Neutree/Gimbal/embedded/demo/MDK/offchip/stm32103c8t6/app/Gimbal.cpp

#include "Gimbal.h"


Gimbal::Gimbal(InertialSensor& ins,Magnetometer& mag,BLDCMotor& motorRoll,BLDCMotor& motorPitch,BLDCMotor& motorYaw,ADC& adc,uint8_t voltageChannel,uint8_t yawResChannel,flash& flash_)
:mIns(ins),mMag(&mag),mMotorRoll(motorRoll),mMotorPitch(motorPitch),mMotorYaw(motorYaw),mADC(adc),mParameter(flash_),mVoltageChannel(voltageChannel),mYawValueChannel(yawResChannel),mIsGyroCalibrating(false),mYawMode(1)
{
	mIsArmed = false;
	mTargetAngle(0,0,0);
	mTargetAngleTemp(0,0,0);
}
bool Gimbal::Init(uint8_t yawSensorType)
{
	float time = TaskManager::Time();
	bool isInitSuccess=true;
	if(!mIns.Init(true))
		isInitSuccess = false;
	//初始化磁力计
	if(!mMag->Init(true))
		isInitSuccess = false;
	
	//从flash中读取参数
	if(!ReadParam2Flash())
	{
		mPIDRoll(5,0.2,0.6);
		mPIDPitch(5,0.1,0.2);
		mPIDYaw(5,0.1,0.1);
		mIns.SetGyrOffset(0,0,0);
		mMag->SetOffsetRatio(1.285,1.285,1);
		mMag->SetOffsetBias(236,309,114);
		//保存信息到flash
		SaveParam2Flash();
	}
	CheckMotorDisable();
	mYawSensorType = yawSensorType;
	if(mYawSensorType == 1)
		mYawAngleRes = GetYawValue()/(2.3-0.35)*260.0 ;
	return isInitSuccess;
}
bool Gimbal::UpdateIMU()
{
	if(MOD_ERROR== mIns.Update())
	{
		LOG("mpu6050 error\n\n\n");
		return false;
	}
	if(mMag!=0)
	{
		if(MOD_ERROR == mMag->Update())
		{
			LOG("MAG error\n\n\n");
			return false;
		}
	}
	if(mIsGyroCalibrating&&mIns.IsGyroCalibrated())//角速度校准刚结束
	{
		mIsGyroCalibrating = false;
		LOG("\ngyro calibrate complete\n");
		SaveParam2Flash();
		mMotorRoll.Enable();
		mMotorPitch.Enable();
		mMotorYaw.Enable();
	}
	
	if(mIsMagCalibrating&&mMag->IsCalibrated())//磁力计校准刚结束
	{
		mIsMagCalibrating = false;
		LOG("\nmagnetometer calibrate complete\n");
		SaveParam2Flash();
	}
	
	if(mIns.IsGyroCalibrated())//角速度和磁力计已经校准了
	{		
		if(mYawSensorType==1)//电位器+加速度角速度计
		{
//				mAngle = mAHRS_Algorithm.GetAngleMahony(mIns.GetAccRaw(),mIns.GetGyr(),mMag->GetDataRaw(),mIns.GetUpdateInterval());
//			Vector3<int> mag0(0,0,0);
//			mAngle = mAHRS_Algorithm.GetAngleMahony(mIns.GetAccRaw(),mIns.GetGyr(),mag0,mIns.GetUpdateInterval());
			mAngle = mAHRS_Algorithm.GetAngleDCM(mIns.GetAcc(),mIns.GetGyr(),mIns.GetUpdateInterval());
			if(mYawMode == 2)//静止模式
			{
				mYawAngleRes = mYawAngleRes*0.998 + ( GetYawValue()/(2.3-0.35)*260.0 )*0.002;//高斯滤波
				mAngle.z = mYawAngleRes;
			}
			else if(mYawMode == 1)//跟随模式
			{

				mYawAngleRes = mYawAngleRes*0.998 + ( GetYawValue()/(2.3-0.35)*260.0 )*0.002;//高斯滤波
				mAngle.z = mYawAngleRes;
			}
			else if(mYawMode ==  3)//绝对静止模式
			{
				
			}
		}
		else if(mYawSensorType==2)//电位器+IMU+磁力计
		{
			if(mMag->IsCalibrated())
			{
					mAngle = mAHRS_Algorithm.GetAngleMahony(mIns.GetAccRaw(),mIns.GetGyr(), mMag->GetDataRaw(),mIns.GetUpdateInterval());
			}
		}
		//根据传感器安装方位进行换向
		mAngle.z = -mAngle.z;
//		mAngle.y>0?(mAngle.y-=180):(mAngle.y+=180);
//		mAngle.y = -mAngle.y;
		mAngle.z>0?(mAngle.z-=180):(mAngle.z+=180);
		
		//转换为弧度
		mAngle*=AtR;
//		mAngle2*=AtR;
	}
	return true;
}
float Gimbal::GetYawValue()
{
	return mADC[mYawValueChannel];
}
bool Gimbal::UpdateMotor(int* motorRollValue,int* motorPitchValue, int* motorYawValue)
{
	static int v=0,v2=0,v3=0;
	mTargetAngleTemp = mTargetAngleTemp*0.998 + mTargetAngle*0.002;
	v  = mPIDRoll.Controll(mTargetAngleTemp.y,mAngle.y);
	v2 = mPIDPitch.Controll(mTargetAngleTemp.x,mAngle.x);
	if(mYawMode == 2)//相对静止模式
		v3 = mPIDYaw.Controll(mTargetAngleTemp.z,mAngle.z);
	else if(mYawMode == 1)//跟随模式
	{
		//根据云台的姿态求出z轴的角速度
		float yawVel = cos(mAngle.y)*cos(mAngle.x)*mIns.GetGyr().z - mIns.GetGyr().y*sin(mAngle.y) + mIns.GetGyr().x*sin(mAngle.y)*sin(mAngle.x);
		static float kd=0;
		kd=mPIDYaw.mKd;
		mPIDYaw.mKd = 0;
		yaw__ = yawVel*kd*100;
		v3 = mPIDYaw.Controll(mTargetAngle.z,mAngle.z)+yaw__;
		mPIDYaw.mKd = kd;
	}
	else if(mYawMode == 3)//绝对静止模式
	{
		
	}
	v3=-v3;
	if(mMotorRoll.IsEnabled())
		mMotorRoll.SetPosition(v);
	if(mMotorPitch.IsEnabled())
		mMotorPitch.SetPosition(v2);
	if(mMotorYaw.IsEnabled())
		mMotorYaw.SetPosition(v3);
	
	if(motorRollValue!=0)
		*motorRollValue = v;
	if(motorPitchValue!=0)
		*motorPitchValue = v2;
	if(motorYawValue!=0)
		*motorYawValue = v3;
	return true;
}
float Gimbal::UpdateVoltage(float resister_a,float resister_b,float fullRange)
{
	return mADC.Voltage_I(mVoltageChannel,resister_a,resister_b,fullRange);
}
bool Gimbal::IsGyroCalibrated()
{
	return mIns.IsGyroCalibrated();
}
bool Gimbal::IsGyroCalibrating()
{
	return mIsGyroCalibrating;
}
void Gimbal::StartGyroCalibrate()
{
	mMotorRoll.Disable();
	mMotorPitch.Disable();
	mMotorYaw.Disable();
	float time = TaskManager::Time();
	while(TaskManager::Time()-time<2.5)
	{
		if(MOD_ERROR== mIns.Update())
		{
			LOG("mpu6050 error\n\n\n");
			return;
		}
		if(mMag!=0)
		{
			if(MOD_ERROR == mMag->Update())
			{
				LOG("MAG error\n\n\n");
				return ;
			}
		}
		TaskManager::DelayMs(100);
	}	
	mIns.StartGyroCalibrate();//启动校准
	mIsGyroCalibrating = true;
	LOG("start gyro calibrate, don't move\n");
}
bool Gimbal::IsMagCalibrated()
{
	return mMag->IsCalibrated();
}
bool Gimbal::IsMagCalibrating()
{
	return mIsMagCalibrating;
}
void Gimbal::StartMagCalibrate()
{
	mMag->StartCalibrate();//启动校准
	mIsMagCalibrating = true;
	LOG("magnetometer is calibrating ... don't move!!!\n");
}
void Gimbal::CheckMotorDisable()
{
	if(mMotorRoll.IsEnabled())
	{
		if(mPIDRoll.mKp==0 && mPIDRoll.mKi==0 && mPIDRoll.mKd==0)
		{
			mPIDRoll.Clear();
			mMotorRoll.Disable();
		}
	}
	else
	{
		if(mPIDRoll.mKp!=0 || mPIDRoll.mKi!=0 || mPIDRoll.mKd!=0)
			mMotorRoll.Enable();
	}
	if(mMotorPitch.IsEnabled())
	{
		if(mPIDPitch.mKp==0 && mPIDPitch.mKi==0 && mPIDPitch.mKd==0)
		{
			mPIDPitch.Clear();
			mMotorPitch.Disable();
		}
	}
	else
	{
		if(mPIDPitch.mKp!=0 || mPIDPitch.mKi!=0 || mPIDPitch.mKd!=0)
			mMotorPitch.Enable();
	}
	if(mMotorYaw.IsEnabled())
	{
		if(mPIDYaw.mKp==0 && mPIDYaw.mKi==0 && mPIDYaw.mKd==0)
		{
			mPIDYaw.Clear();
			mMotorYaw.Disable();
		}
	}
	else
	{
		if(mPIDYaw.mKp!=0 || mPIDYaw.mKi!=0 || mPIDYaw.mKd!=0)
			mMotorYaw.Enable();
	}
}
bool Gimbal::SaveParam2Flash()
{
	// u16 data[20];
	// data[0] = 0x00aa;
	// data[1] = 0x00bb;
	// data[2] = mPIDRoll.mKp*1000;
	// data[3] = mPIDRoll.mKi*1000;
	// data[4] = mPIDRoll.mKd*1000;
	// data[5] = mPIDPitch.mKp*1000;
	// data[6] = mPIDPitch.mKi*1000;
	// data[7] = mPIDPitch.mKd*1000;
	// data[8] = mPIDYaw.mKp*1000;
	// data[9] = mPIDYaw.mKi*1000;
	// data[10] = mPIDYaw.mKd*1000;
	// data[11] = mIns.GetGyrOffset().x+32768;
	// data[12] = mIns.GetGyrOffset().y+32768;
	// data[13] = mIns.GetGyrOffset().z+32768;
	// data[14] = mMag->GetOffsetRatio().x*10000;
	// data[15] = mMag->GetOffsetRatio().y*10000;
	// data[16] = mMag->GetOffsetRatio().z*10000;
	// data[17] = mMag->GetOffsetBias().x+32768;
	// data[18] = mMag->GetOffsetBias().y+32768;
	// data[19] = mMag->GetOffsetBias().z+32768;
	// mFlash.Clear(0);
	// if(!mFlash.Write(0,0,data,20))
	// 	return false;
	// ReadParam2Flash();
	CheckMotorDisable();
	mPIDYaw.mKp*=0.01;
	mPIDYaw.mKi*=0.01;
	mPIDYaw.mKd*=0.01;
	return mParameter.SaveParam2Flash(mPIDRoll,mPIDPitch,mPIDYaw,mIns.GetGyrOffset(),mMag->GetOffsetRatio(),mMag->GetOffsetBias());
}

bool Gimbal::ReadPIDParam2Flash()
{
	// u16 data[11];
	// if(!mFlash.Read(0,0,data,11))
	// 	return false;
	// if(data[0]!=0x00aa || data[1]!=0x00bb)
	// 	return false;
	// mPIDRoll.SetKp(data[2]/1000.0);
	// mPIDRoll.SetKi(data[3]/1000.0);
	// mPIDRoll.SetKd(data[4]/1000.0);
	// mPIDPitch.SetKp(data[5]/1000.0);
	// mPIDPitch.SetKi(data[6]/1000.0);
	// mPIDPitch.SetKd(data[7]/1000.0);
	// mPIDYaw.SetKp(data[8]/1000.0);
	// mPIDYaw.SetKi(data[9]/1000.0);
	// mPIDYaw.SetKd(data[10]/1000.0);
	return false;
}
bool Gimbal::ReadGyroOffset2Flash()
{
	// u16 data[3];
	// if(!mFlash.Read(0,0,data,2))
	// 	return false;
	// if(data[0]!=0x00aa || data[1]!=0x00bb)
	// 	return false;
	// if(!mFlash.Read(0,11,data,3))
	// 	return false;
	// Vector3<int> gyroOffset;
	// gyroOffset.x = data[0]-32768;
	// gyroOffset.y = data[1]-32768;
	// gyroOffset.z = data[2]-32768;
	// mIns.SetGyrOffset(gyroOffset.x,gyroOffset.y,gyroOffset.z); 
	return false;
}
//磁力计校准值储存
bool Gimbal::ReadMagOffset2Flash()
{
	// u16 data[6];
	// if(!mFlash.Read(0,0,data,2))
	// 	return false;
	// if(data[0]!=0x00aa || data[1]!=0x00bb)
	// 	return false;
	// if(!mFlash.Read(0,14,data,6))
	// 	return false;
	// Vector3f magOffsetRatio,magOffsetBias;
	// magOffsetRatio.x = data[0]/10000.0;
	// magOffsetRatio.y = data[1]/10000.0;
	// magOffsetRatio.z = data[2]/10000.0;
	// magOffsetBias.x = data[3]-32768;
	// magOffsetBias.y = data[4]-32768;
	// magOffsetBias.z = data[5]-32768;
	// mMag->SetOffsetRatio(magOffsetRatio.x,magOffsetRatio.y,magOffsetRatio.z); 
	// mMag->SetOffsetBias(magOffsetBias.x,magOffsetBias.y,magOffsetBias.z);
	return false;
}

bool Gimbal::ReadParam2Flash()
{
	// u16 data[20];
	// if(!mFlash.Read(0,0,data,20))
	// 	return false;
	// if(data[0]!=0x00aa || data[1]!=0x00bb)
	// 	return false;
	// mPIDRoll.SetKp(data[2]/1000.0);
	// mPIDRoll.SetKi(data[3]/1000.0);
	// mPIDRoll.SetKd(data[4]/1000.0);
	// mPIDPitch.SetKp(data[5]/1000.0);
	// mPIDPitch.SetKi(data[6]/1000.0);
	// mPIDPitch.SetKd(data[7]/1000.0);
	// mPIDYaw.SetKp(data[8]/1000.0);
	// mPIDYaw.SetKi(data[9]/1000.0);
	// mPIDYaw.SetKd(data[10]/1000.0);
	// Vector3<int> gyroOffset;
	// gyroOffset.x = data[11]-32768;
	// gyroOffset.y = data[12]-32768;
	// gyroOffset.z = data[13]-32768;
	// mIns.SetGyrOffset(gyroOffset.x,gyroOffset.y,gyroOffset.z); 
	// Vector3f magOffsetRatio,magOffsetBias;
	// magOffsetRatio.x = data[14]/10000.0;
	// magOffsetRatio.y = data[15]/10000.0;
	// magOffsetRatio.z = data[16]/10000.0;
	// magOffsetBias.x = data[17]-32768;
	// magOffsetBias.y = data[18]-32768;
	// magOffsetBias.z = data[19]-32768;
	// mMag->SetOffsetRatio(magOffsetRatio.x,magOffsetRatio.y,magOffsetRatio.z); 
	// mMag->SetOffsetBias(magOffsetBias.x,magOffsetBias.y,magOffsetBias.z);
	Vector3<int> gyroOffset;
	Vector3f magOffsetRatio,magOffsetBias;
	if(!mParameter.ReadParamFromFlash(mPIDRoll,mPIDPitch,mPIDYaw,gyroOffset,magOffsetRatio,magOffsetBias))
		return false;
	mIns.SetGyrOffset(gyroOffset.x,gyroOffset.y,gyroOffset.z);
	mMag->SetOffsetRatio(magOffsetRatio.x,magOffsetRatio.y,magOffsetRatio.z);
	mMag->SetOffsetBias(magOffsetBias.x,magOffsetBias.y,magOffsetBias.z);
	CheckMotorDisable();
	return true;
}
